Gregwar/eFlute/3d/v1.1/side.stl

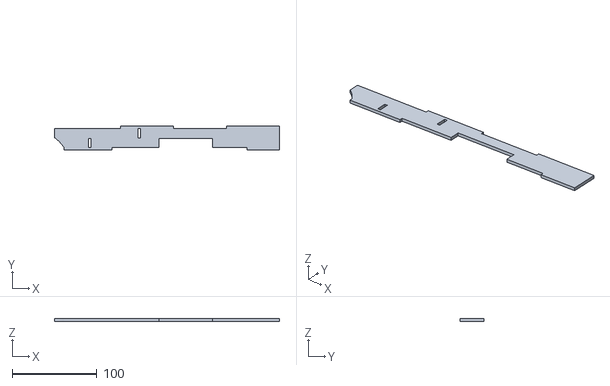
[picture p16: CAD file, 2016-01-20, an earlier design]
3d/v1.1/side.stl
265.0 x 28.0 x 3.00
