Gregwar/eFlute/3d/v1/bottom2.stl

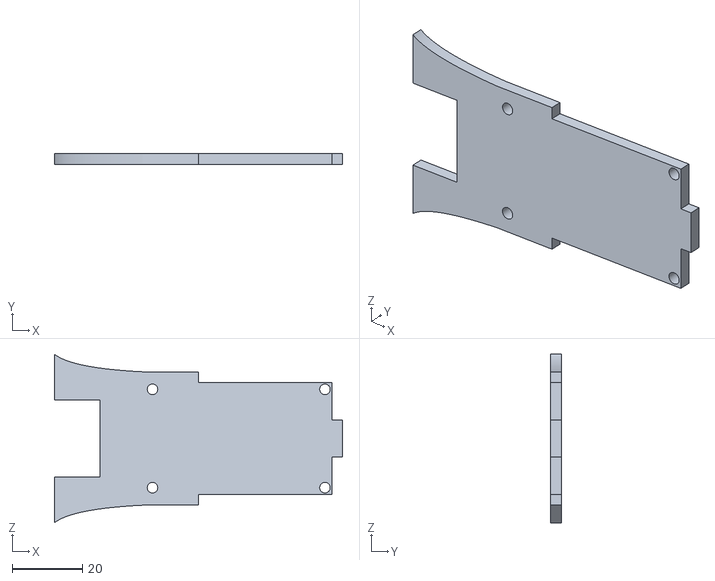
[picture p17: CAD file, 2016-01-20, an earlier design]
3d/v1/bottom2.stl
82.0 x 3.00 x 48.0
