Gregwar/eFlute/3d/v1.1/bottom.stl

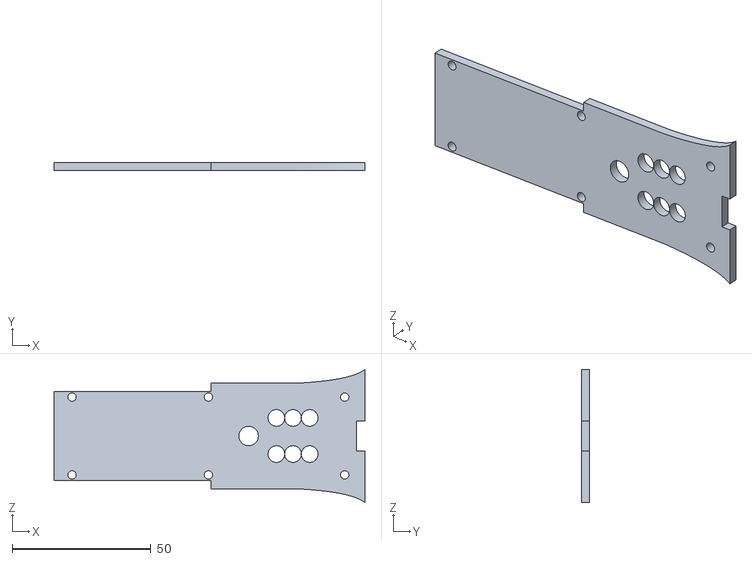
[picture p18: CAD file, 2016-01-20, an earlier design]
3d/v1.1/bottom.stl
112.0 x 3.00 x 48.0
