Gregwar/eFlute/firmware/sd.h

// Sign an expression
#define VALUE_SIGN(value, length) \
    ((value < (1<<(length-1))) ? \
    (value) \
    : (value-(1<<length)))

TERMINAL_PARAMETER_INT(vol, "Volume", 100);
TERMINAL_PARAMETER_INT(targetVol, "Volume", 100);

bool playing = false;
HardwareSPI spi(1);
Sd2Card card;
SdVolume volume;
SdFile root;
SdFile file;

TERMINAL_COMMAND(dac, "dac set")
{
    if (argc != 1) {
        terminal_io()->println("Usage: dac [value]");
    } else {
        int value = atoi(argv[0]);
        dac.set(value);
        dac.latch();
    }
}

#include "sin.h"

TERMINAL_COMMAND(sin, "Sinus")
{
    float samp = 0;
    int i = 0;
    while (!SerialUSB.available()) {
        i++;
        if (i >= 50) i = 0;
        dac.set(values[i]*(samp/2)+2000);
        dac.latch();
        delay_us(6);
    }
}

#define SAMPLES_BUF 512
int samples1[SAMPLES_BUF];
int samples2[SAMPLES_BUF];
int samples_buffer = 1;
int samples_position = 0;
bool should_fill = false;

void interrupt()
{
    dac.latch();
    if (samples_position < 0) {
        samples_position = SAMPLES_BUF-1;
        should_fill = true;
        if (samples_buffer == 1) {
            samples_buffer = 2;
        } else {
            samples_buffer = 1;
        }
    }
    if (samples_buffer == 1) {
        dac.set(2000+(samples1[samples_position--]/(16000/vol)));
    } else {
        dac.set(2000+(samples2[samples_position--]/(16000/vol)));
    }
    if (vol < targetVol) vol++;
    if (vol > targetVol) vol--;
}

void fillBuffer(int *samples)
{
    char buffer[SAMPLES_BUF*2];
    file.read(buffer, SAMPLES_BUF*2);

    for (int k=0; k<SAMPLES_BUF; k++) {
        int sample = (buffer[2*k]&0xff);
        sample |= (buffer[2*k+1]&0xff)<<8;
        sample = VALUE_SIGN(sample, 16);
        samples[SAMPLES_BUF-k-1] = sample;
    }
}

void populateSamples()
{
    if (should_fill) {
        should_fill = false;
        if (samples_buffer == 1) {
            fillBuffer(samples2);
        } else {
            fillBuffer(samples1);
        }
    }
}

TERMINAL_COMMAND(sd, "Sd init")
{
    spi.begin(SPI_18MHZ, MSBFIRST, 0);
    if (card.init(&spi)) {
        terminal_io()->println("Success in card init");
        delay(100);
        if (volume.init(&card,1)) {
            terminal_io()->println("Volume mounted");
            if (root.openRoot(&volume)) {
                terminal_io()->println("Root opened");
            }
        }
    }
}

TERMINAL_COMMAND(play, "Play a sound")
{
    if (argc != 1) {
        terminal_io()->println("Usage: play sound.raw");
    } else {
        playing = false;
        if (file.isOpen()) file.close();
        if (file.open(&root, argv[0], O_READ)) {
            HardwareTimer timer(1);
            timer.pause();
            timer.setPrescaleFactor(1);
            timer.setOverflow(6250);
            //timer.setOverflow(2250);
            //timer.setOverflow(1632);
            timer.setCompare(TIMER_CH1, 1);
            timer.attachCompare1Interrupt(interrupt);
            timer.refresh();
            timer.resume();

            playing = true;

            /*
            for (int k=0; k<64; k++) {
                terminal_io()->println((int)getSample());
            }
            */
        }
    }
}

TERMINAL_COMMAND(card, "Card")
{
    digitalWrite(HOLES_EN, HIGH);
    while (!SerialUSB.available()) {
        terminal_io()->println(analogRead(HOLE1));
        delay(5);
    }
}
