Gregwar/eFlute/firmware/dyn.h

#ifndef _DYN_H
#define _DYN_H

#include "samples.h"
#define DYN
#define DYN_SIZE        16

void set_freq(float v);
void set_tr(int v);
void set_scale(int v);

extern struct sample dyn[DYN_SIZE];
void dyn_gen();
void dyn_init();

#endif
