Gregwar/eFlute/firmware/sin.h

float values[50] = {
0, 0.1253332335643, 0.24868988716485, 0.36812455268468, 0.48175367410172, 0.58778525229247, 0.68454710592869, 0.77051324277579, 0.84432792550202, 0.90482705246602, 
0.95105651629515, 0.98228725072869, 0.99802672842827, 0.99802672842827, 0.98228725072869, 0.95105651629515, 0.90482705246602, 0.84432792550201, 0.77051324277579, 0.68454710592869, 
0.58778525229247, 0.48175367410172, 0.36812455268468, 0.24868988716485, 0.1253332335643, 1.2246467991474E-16, -0.1253332335643, -0.24868988716486, -0.36812455268468, -0.48175367410171, 
-0.58778525229247, -0.68454710592869, -0.77051324277579, -0.84432792550202, -0.90482705246602, -0.95105651629515, -0.98228725072869, -0.99802672842827, -0.99802672842827, -0.98228725072869, 
-0.95105651629515, -0.90482705246602, -0.84432792550202, -0.77051324277579, -0.68454710592869, -0.58778525229247, -0.48175367410172, -0.36812455268468, -0.24868988716486, -0.1253332335643
};
