Gregwar/eFlute/firmware/samples.cpp

#include "samples.h"

// c.raw
static const short sample_c_values[2573] = {
943, 3635, 5506, 6541, 9196, 11918, 13557, 14995, 17525, 19301, 
  20752, 22285, 23612, 24186, 24142, 25576, 25876, 27276, 27385, 27633, 
  27518, 27466, 27129, 26063, 25834, 24407, 24306, 22749, 22000, 20353, 
  19301, 17923, 16385, 14666, 13109, 11809, 10123, 8733, 6587, 5751, 
  4157, 3711, 1832, 1108, -1008, -2556, -4883, -6449, -9078, -11530, 
  -13378, -15707, -17372, -20200, -20947, -22820, -24040, -25516, -26590, -27357, 
  -27511, -27286, -26969, -26692, -26061, -25448, -24839, -24319, -23645, -21850, 
  -21433, -19941, -18560, -16702, -15469, -13540, -11287, -9846, -8614, -6591, 
  -5161, -2738, -737, 1408, 3551, 5588, 7393, 9167, 11290, 13766, 
  15281, 17685, 19265, 21299, 22675, 24455, 24633, 25623, 26265, 26555, 
  27152, 27520, 27514, 27189, 27792, 26976, 26855, 26416, 25344, 24215, 
  23443, 21661, 20367, 18727, 17815, 16117, 14838, 13141, 11718, 10506, 
  8973, 7802, 6665, 4697, 3895, 2193, 670, -722, -2520, -3483, 
  -6299, -7691, -10252, -12677, -15319, -17444, -19273, -21052, -22698, -23369, 
  -24335, -26086, -25863, -26998, -27129, -27184, -27303, -26244, -26236, -25290, 
  -24634, -23731, -22056, -21370, -19097, -18423, -16661, -15248, -13261, -12169, 
  -9780, -8402, -6442, -4094, -2585, -268, 2072, 3157, 5398, 7284, 
  9041, 11503, 13727, 15628, 17585, 19746, 20990, 22694, 23636, 24876, 
  25432, 26094, 27196, 26560, 28022, 27573, 28079, 27431, 27144, 26462, 
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
  14327, 10687, 7117, 3226, -469, -4345, -7722, -11249, -14470, -18052, 
  -20701, -23389, -25140, -26636, -27834, -28777, -29555, -30045, -30304, -30544, 
  -30176, -29718, -28332, -26957, -24855, -22445, -19300, -15512, -11230, -6510};
const struct sample sample_a = {sample_a_values, 50};

// b.raw
static const short sample_b_values[46] = {
4157, 9300, 14084, 18775, 22638, 25645, 27932, 29359, 30605, 31435, 
  32519, 32763, 32767, 32593, 31412, 30049, 27102, 23943, 19436, 14673, 
  9241, 4193, -988, -5486, -9691, -13219, -16885, -20683, -24485, -28272, 
  -31630, -32766, -32768, -32765, -32768, -32765, -32133, -30253, -28026, -25339, 
  -21994, -18026, -14035, -9241, -4266, 1011};
const struct sample sample_b = {sample_b_values, 46};

// c2.raw
static const short sample_c2_values[45] = {
484, 5636, 10358, 14611, 18322, 21612, 24774, 27244, 29254, 30707, 
  31379, 31549, 31189, 30527, 28926, 27142, 25124, 22410, 19405, 15509, 
  11304, 6867, 2008, -2776, -7838, -12623, -17177, -20958, -24484, -27628, 
  -30262, -31779, -32687, -32768, -32633, -31722, -30619, -28699, -26274, -23134, 
  -20079, -15561, -11120, -6171, -823};
const struct sample sample_c2 = {sample_c2_values, 45};
